xsrf/ESP-LED-Clock/img/IMG_20181216_120332.jpg

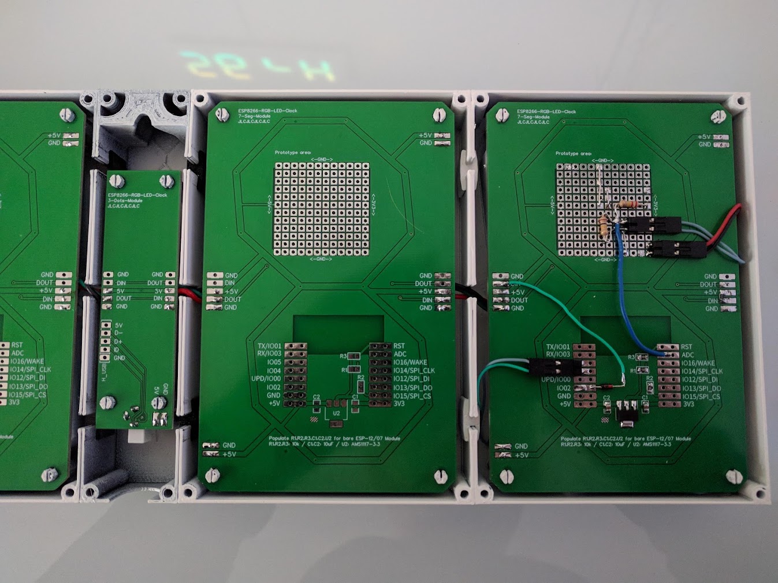
img/IMG_20181216_120332.jpg
