xsrf/ESP-LED-Clock/img/IMG_20181216_120518.jpg

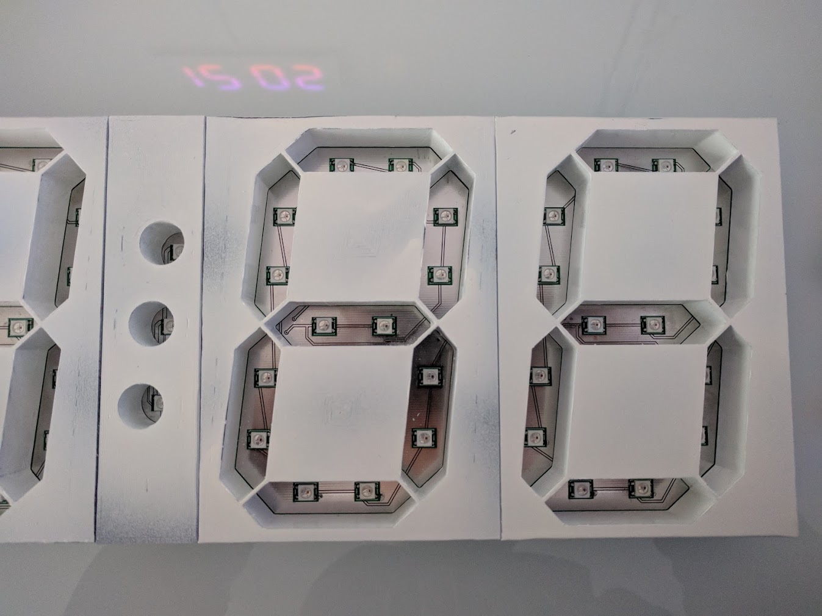
img/IMG_20181216_120518.jpg
