xsrf/ESP-LED-Clock/img/IMG_20181216_120600.jpg

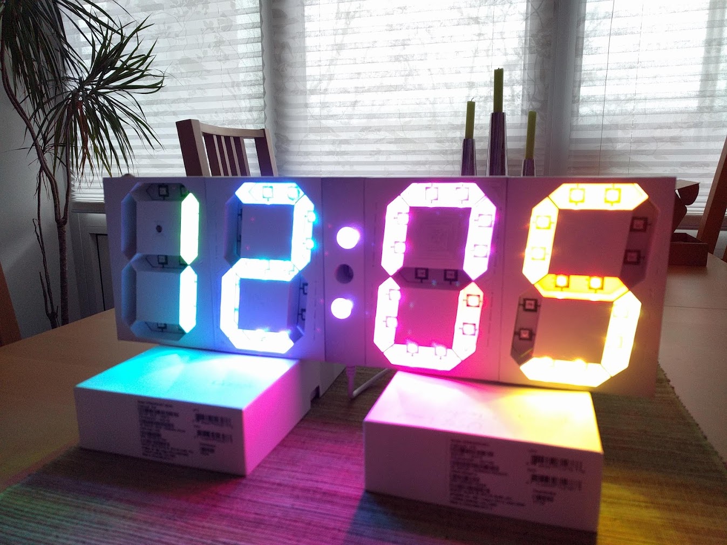
img/IMG_20181216_120600.jpg
