xsrf/ESP-LED-Clock/img/IMG_20200623_143801.jpg

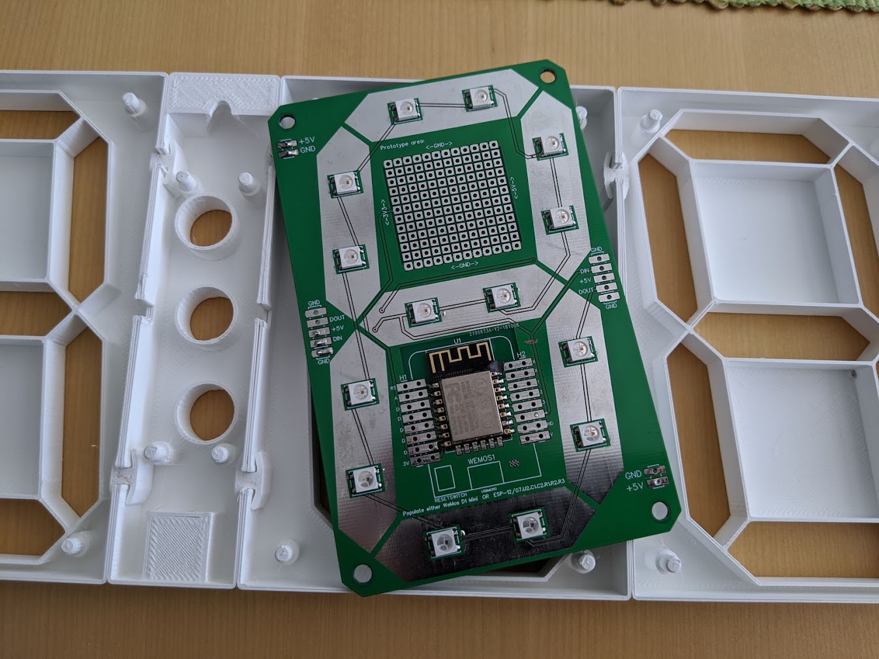
img/IMG_20200623_143801.jpg
