xsrf/ESP-LED-Clock/img/IMG_20200624_115558.jpg

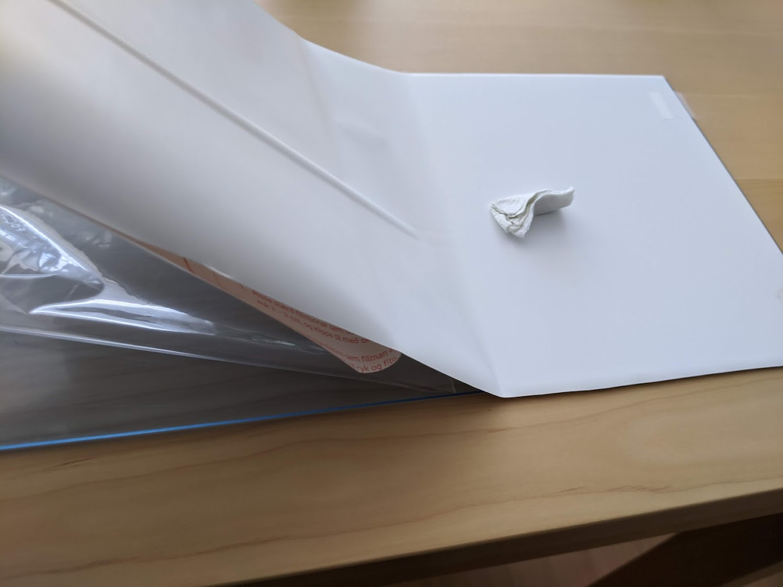
img/IMG_20200624_115558.jpg
