xsrf/ESP-LED-Clock/img/IMG_20200625_190054.jpg

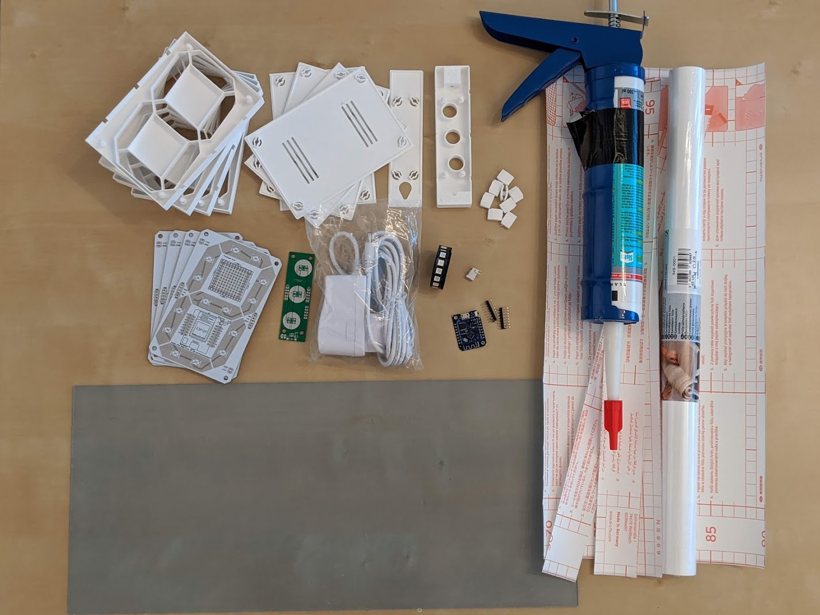
img/IMG_20200625_190054.jpg
