xsrf/ESP-LED-Clock/img/IMG_20200626_114652.jpg

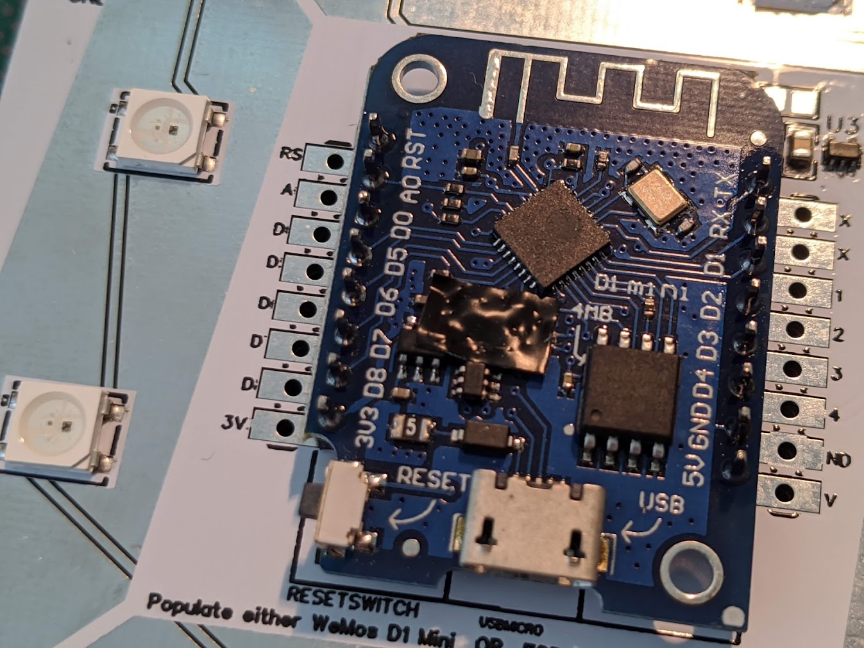
img/IMG_20200626_114652.jpg
